elliotgaler/cyberdeck-2077/documentation/images/Screenshot 2026-04-25 143740.png

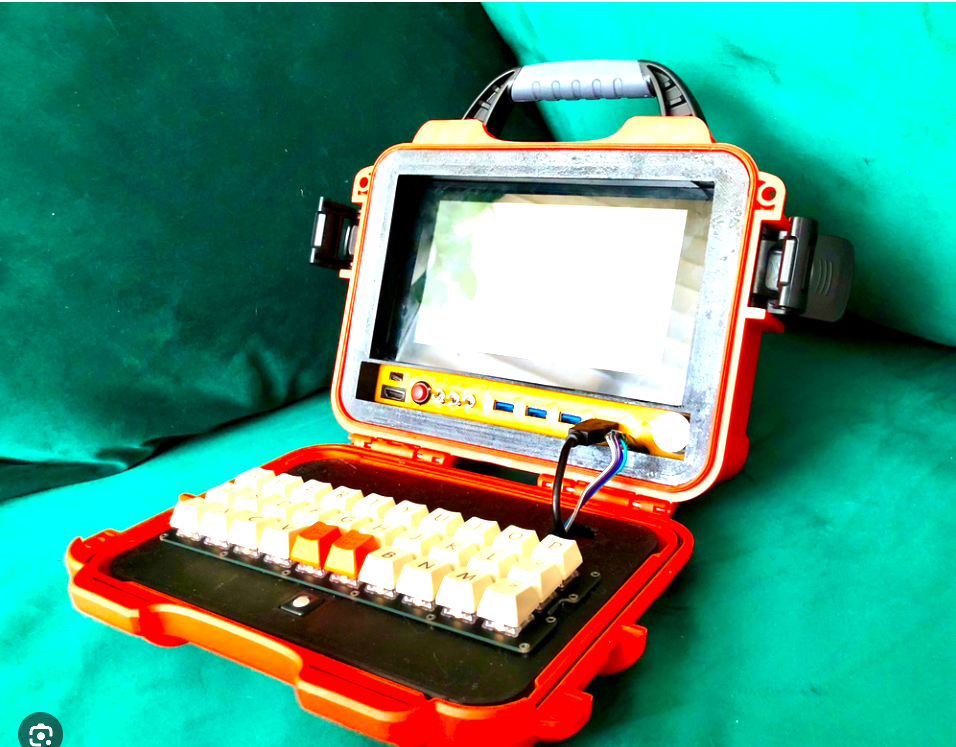
documentation/images/Screenshot 2026-04-25 143740.png
