elliotgaler/cyberdeck-2077/documentation/images/Screenshot 2026-04-25 145606.png

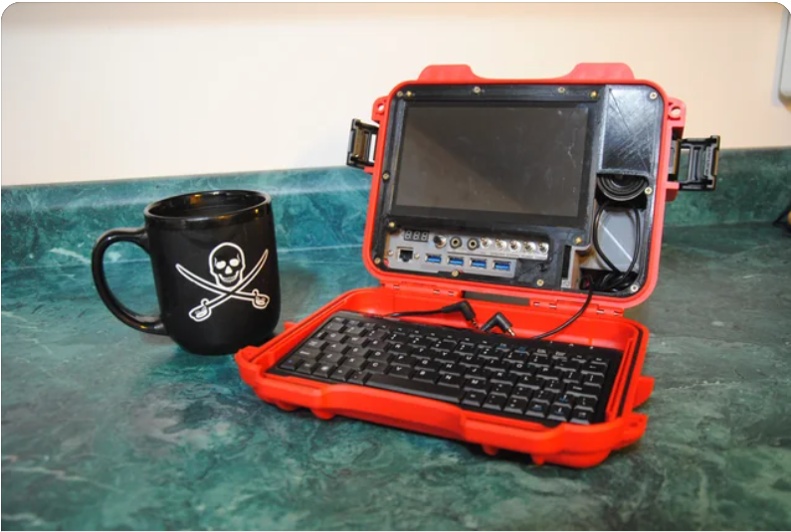
documentation/images/Screenshot 2026-04-25 145606.png
