elliotgaler/cyberdeck-2077/documentation/images/Screenshot 2026-04-25 172017.png

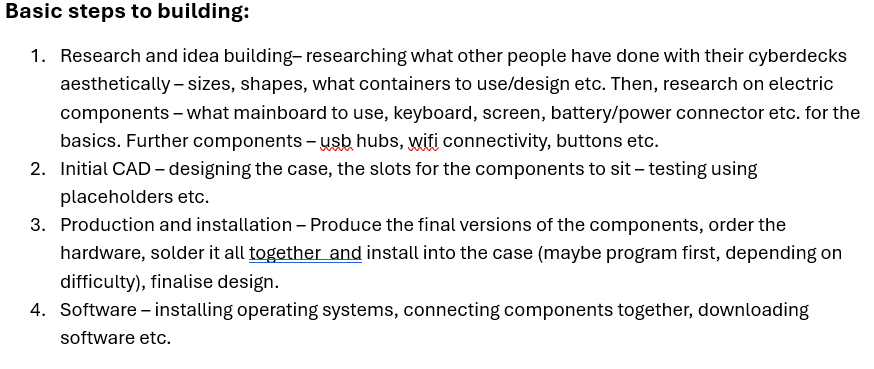
documentation/images/Screenshot 2026-04-25 172017.png
