elliotgaler/cyberdeck-2077/documentation/images/Screenshot 2026-04-26 180212.png

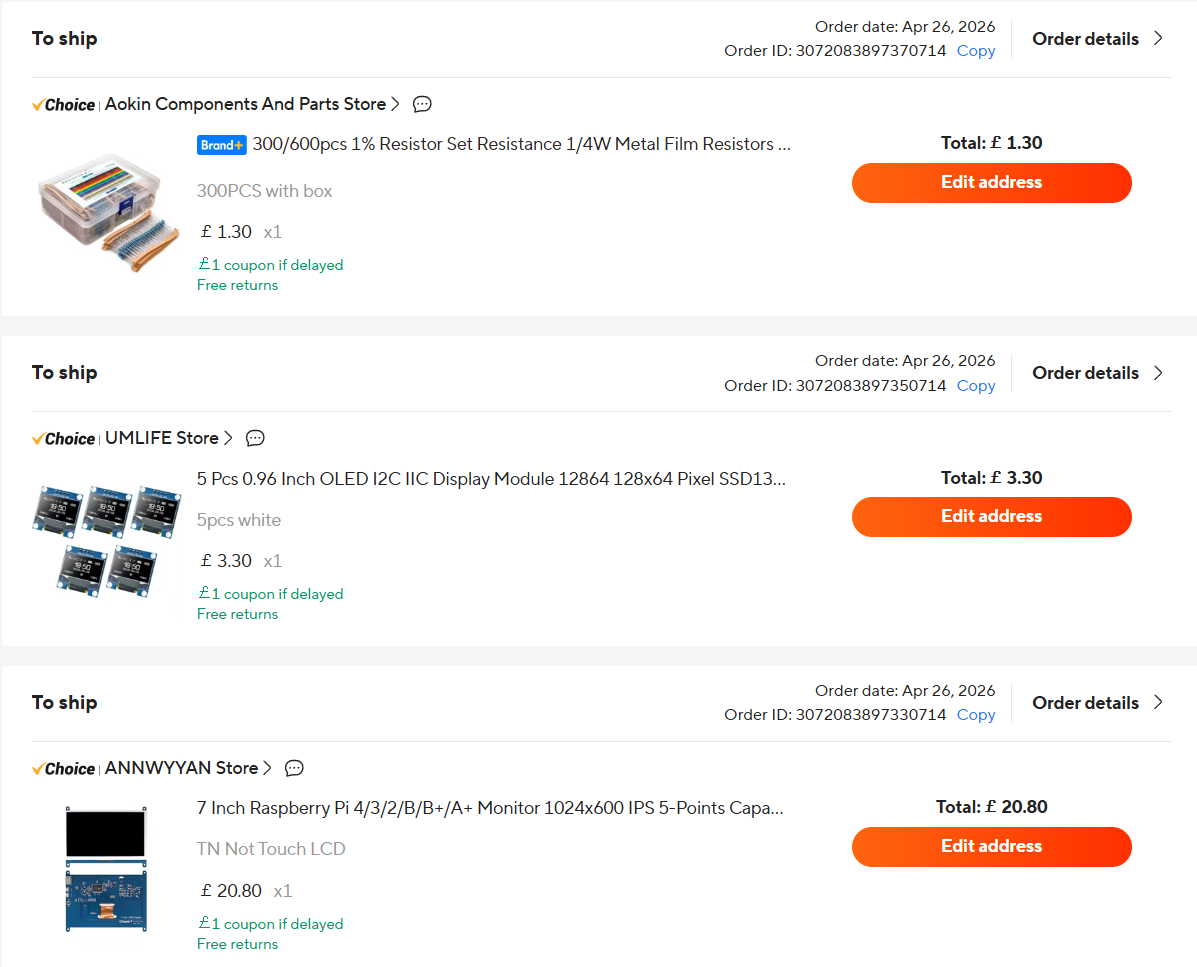
documentation/images/Screenshot 2026-04-26 180212.png
