elliotgaler/cyberdeck-2077/documentation/images/Screenshot 2026-04-28 215603.png

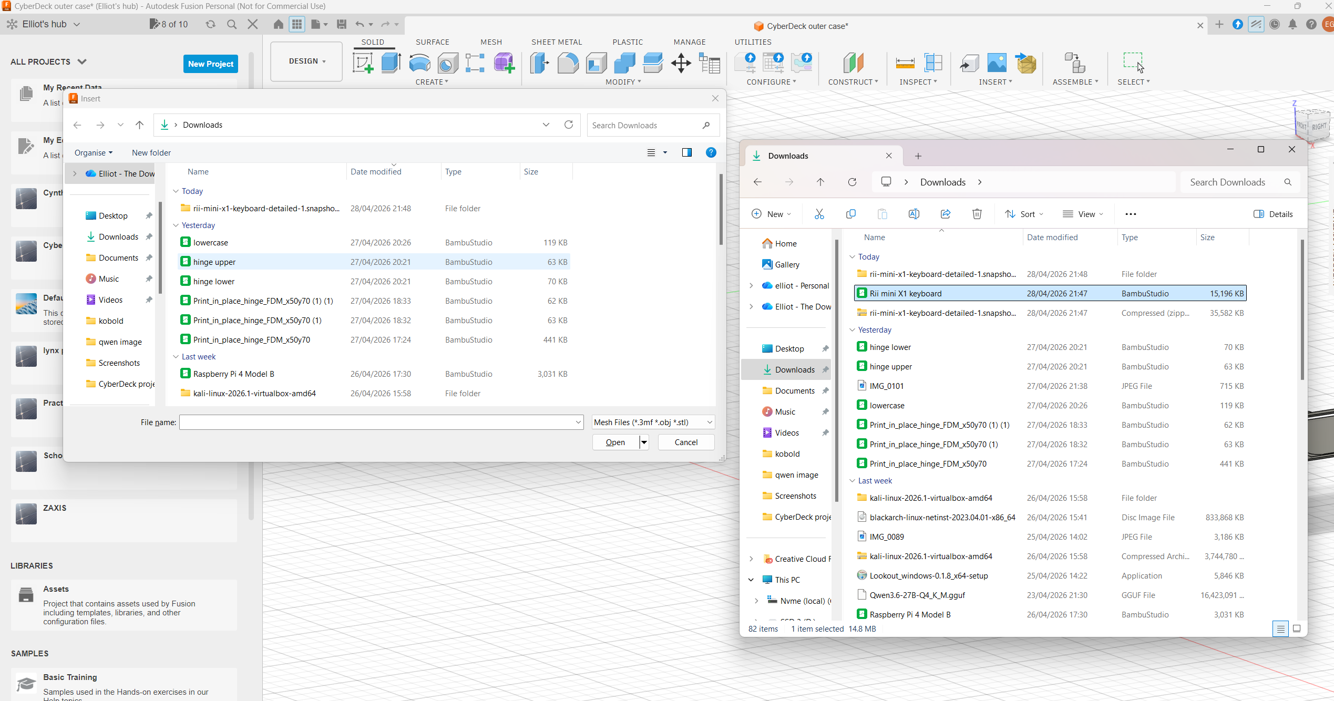
documentation/images/Screenshot 2026-04-28 215603.png
