elliotgaler/cyberdeck-2077/documentation/images/Screenshot 2026-04-29 210022.png

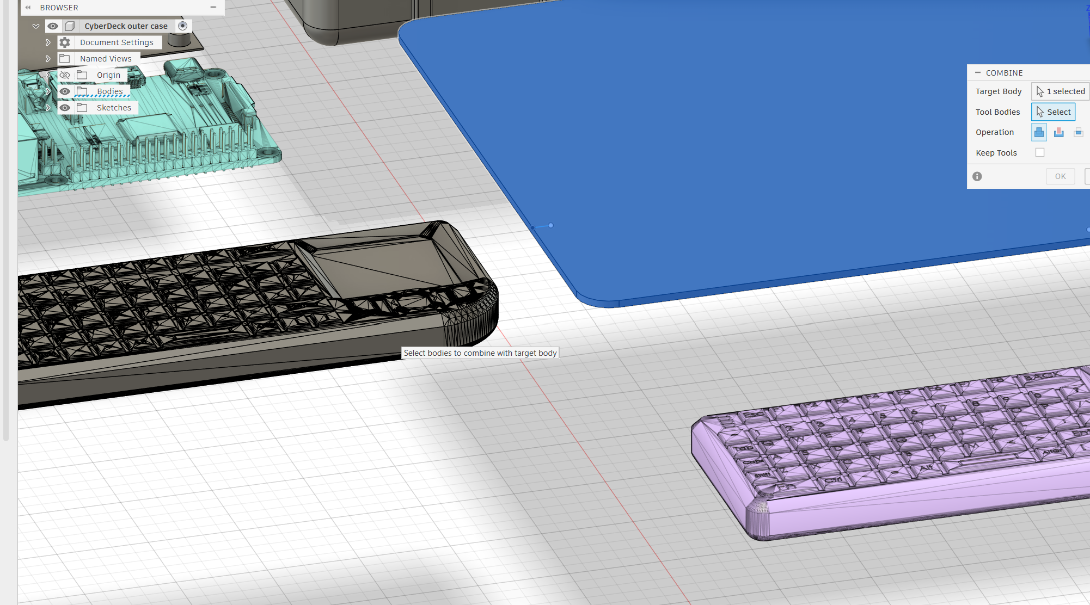
documentation/images/Screenshot 2026-04-29 210022.png
