elliotgaler/cyberdeck-2077/documentation/images/Screenshot 2026-05-03 163417.png

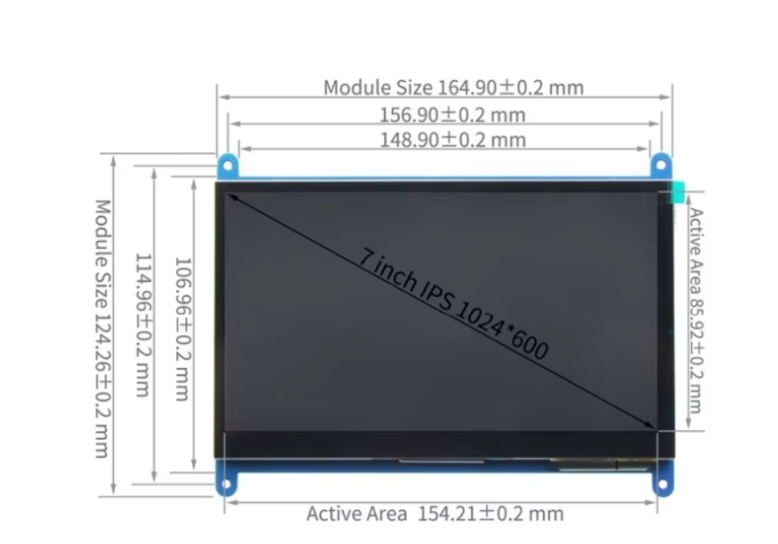
documentation/images/Screenshot 2026-05-03 163417.png
