elliotgaler/cyberdeck-2077/documentation/images/Screenshot 2026-05-04 211452.png

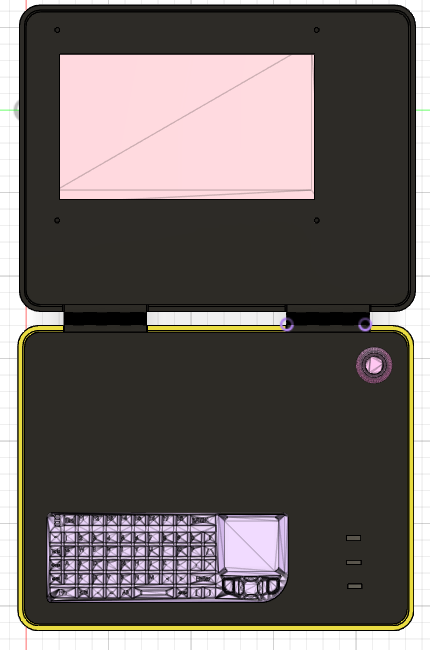
documentation/images/Screenshot 2026-05-04 211452.png
