elliotgaler/cyberdeck-2077/documentation/images/Screenshot 2026-05-05 175409.png

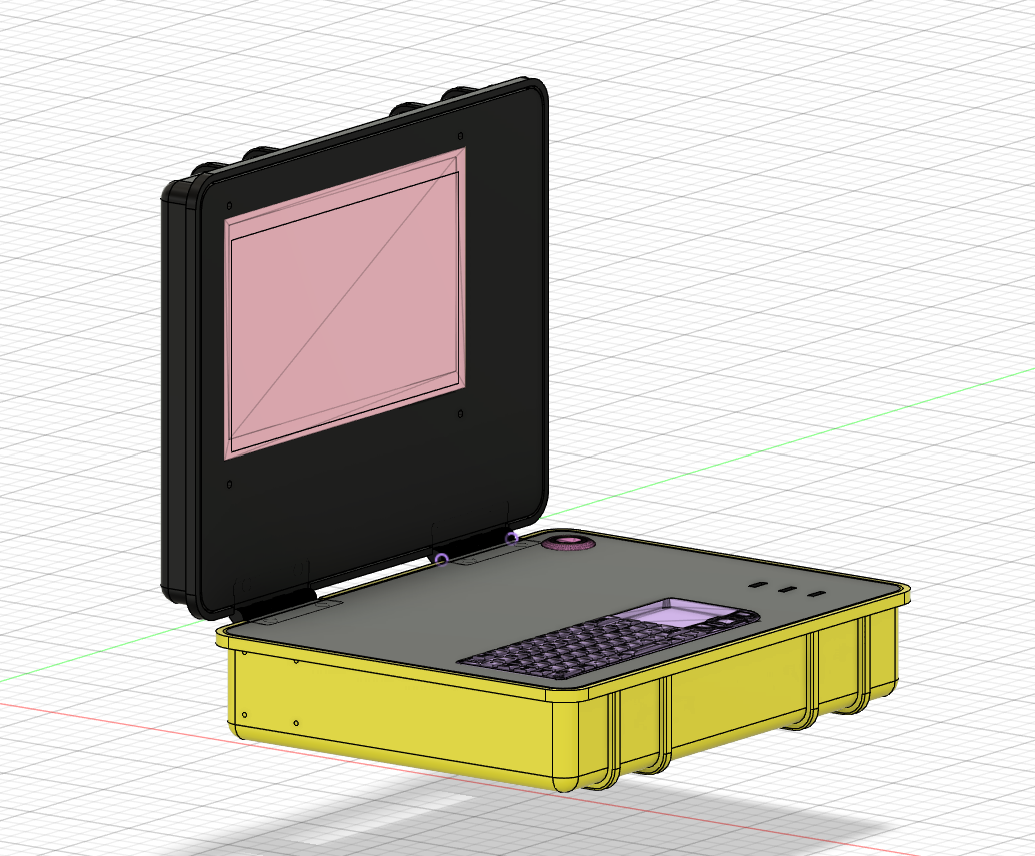
documentation/images/Screenshot 2026-05-05 175409.png
