elliotgaler/cyberdeck-2077/documentation/images/Screenshot 2026-05-06 172015.png

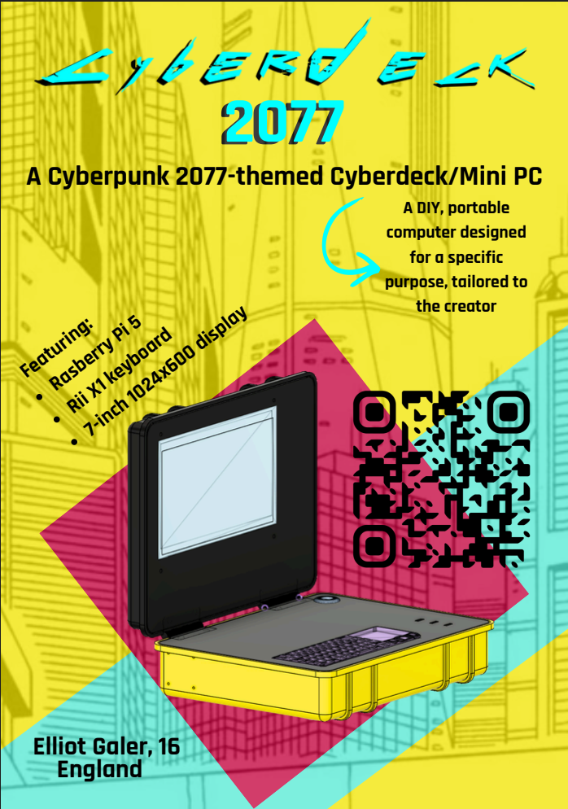
documentation/images/Screenshot 2026-05-06 172015.png
