elliotgaler/cyberdeck-2077/documentation/images/Screenshot 2026-05-06 215000.png

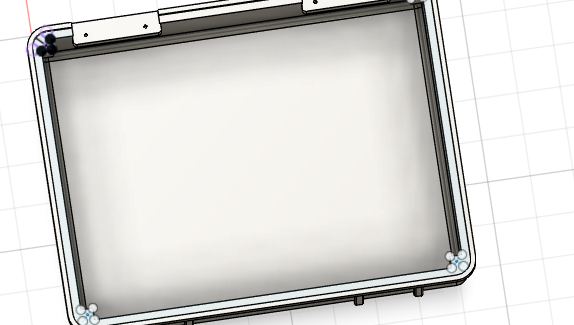
documentation/images/Screenshot 2026-05-06 215000.png
