elliotgaler/cyberdeck-2077/documentation/images/Screenshot 2026-05-19 210840.png

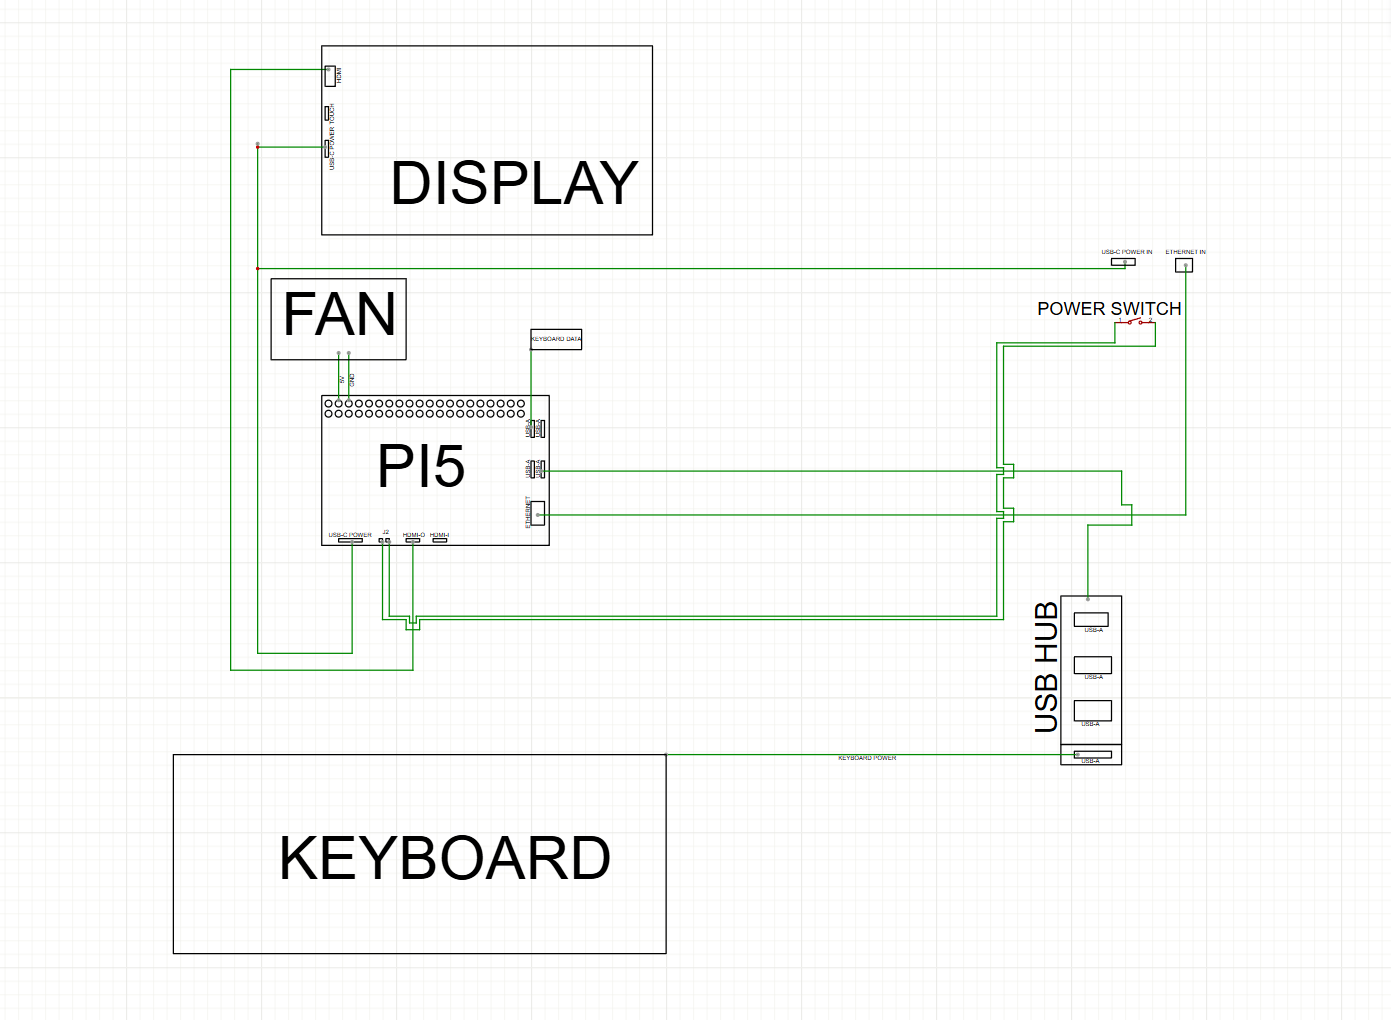
documentation/images/Screenshot 2026-05-19 210840.png
